damianomoscardini/3d-printed-single-photon-diffraction/acquisitions/double-slit/slit-closeup.jpg

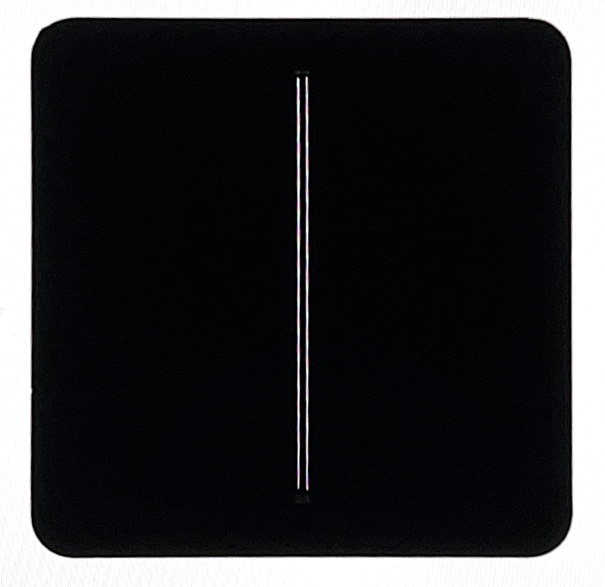
acquisitions/double-slit/slit-closeup.jpg
