damianomoscardini/3d-printed-single-photon-diffraction/acquisitions/single-slit/slit-closeup.jpg

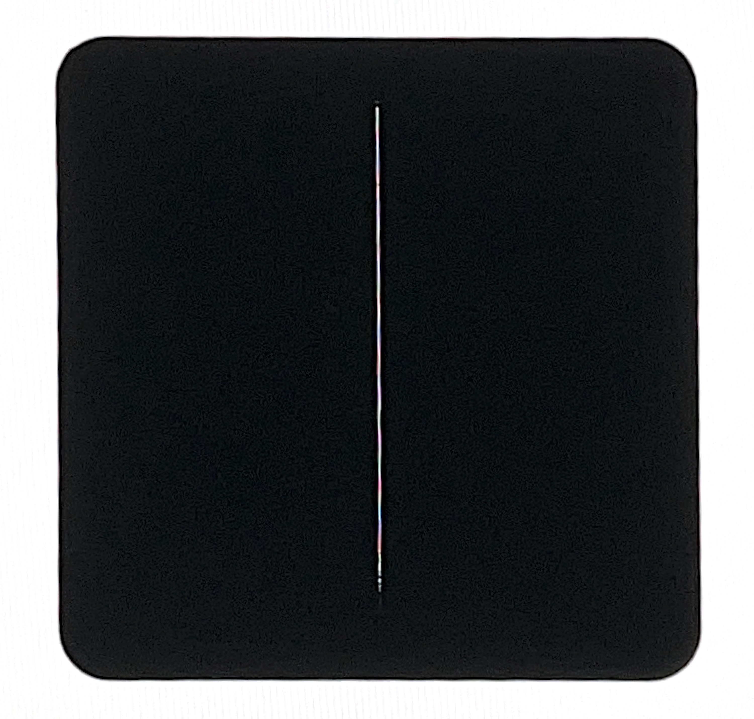
acquisitions/single-slit/slit-closeup.jpg
